TakitaNirasa/mcuDebugBoard/PCB _lite/image_2023-05-27_09-38-56.png

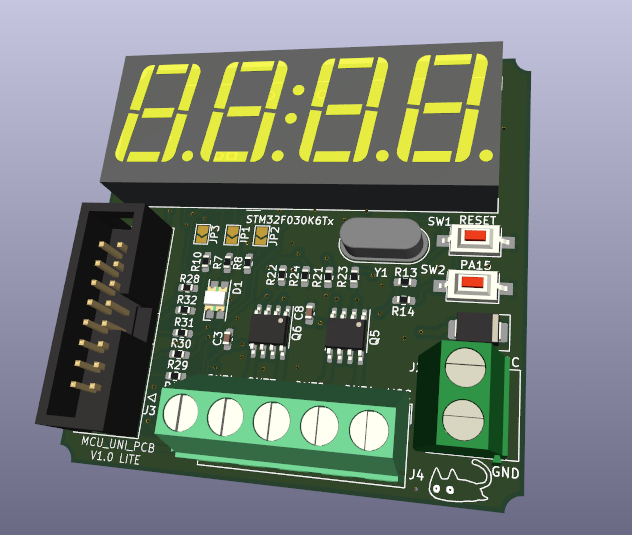
PCB _lite/image_2023-05-27_09-38-56.png
